dmsherazi/Battery-Management-System/gEDA-circuit-breaker/circuit-breaker-1.png

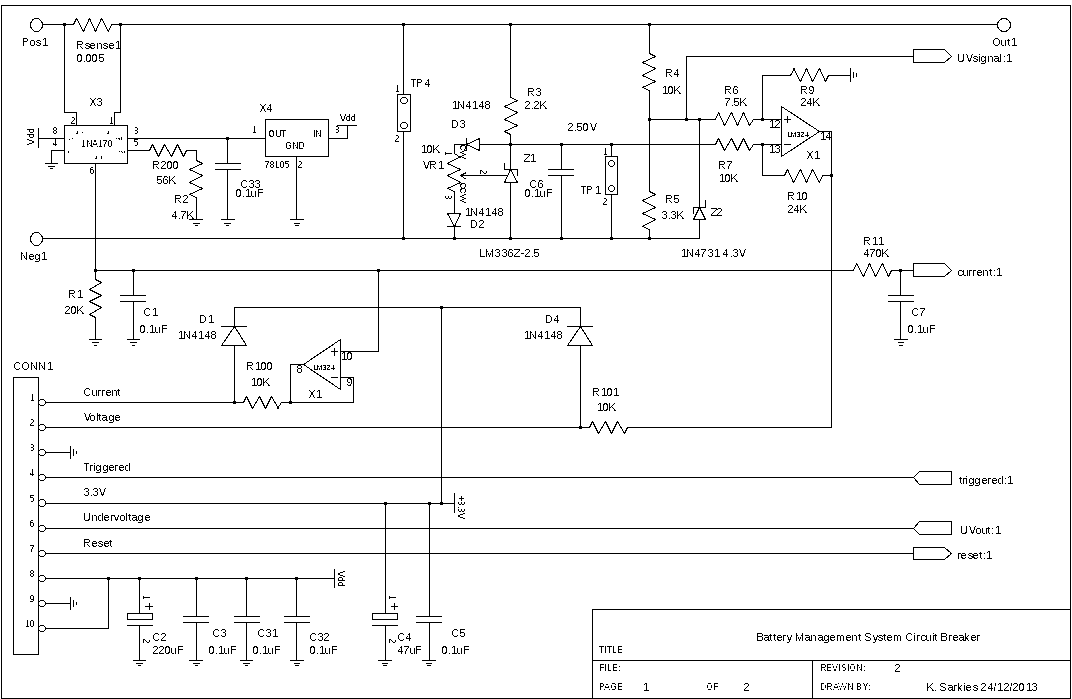
gEDA-circuit-breaker/circuit-breaker-1.png
