dmsherazi/Battery-Management-System/gEDA-circuit-breaker/circuit-breaker-2.png

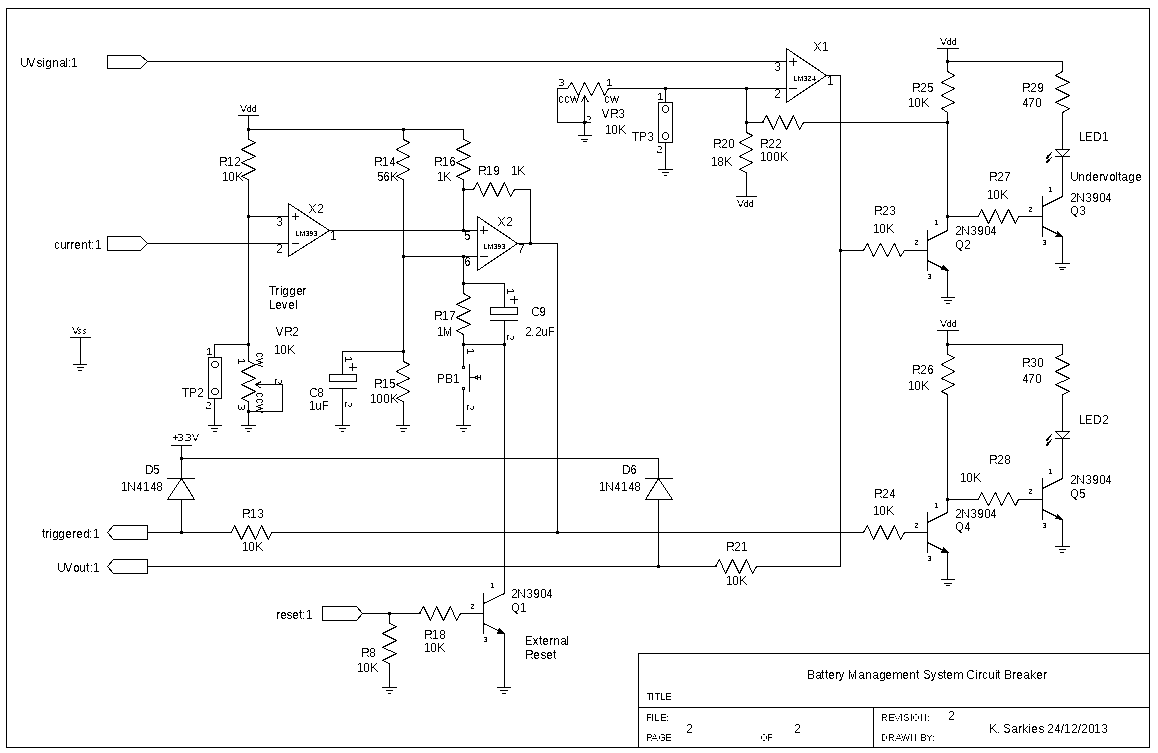
gEDA-circuit-breaker/circuit-breaker-2.png
