dmsherazi/Battery-Management-System/gEDA-circuit-breaker/circuit-breaker-pcb.png

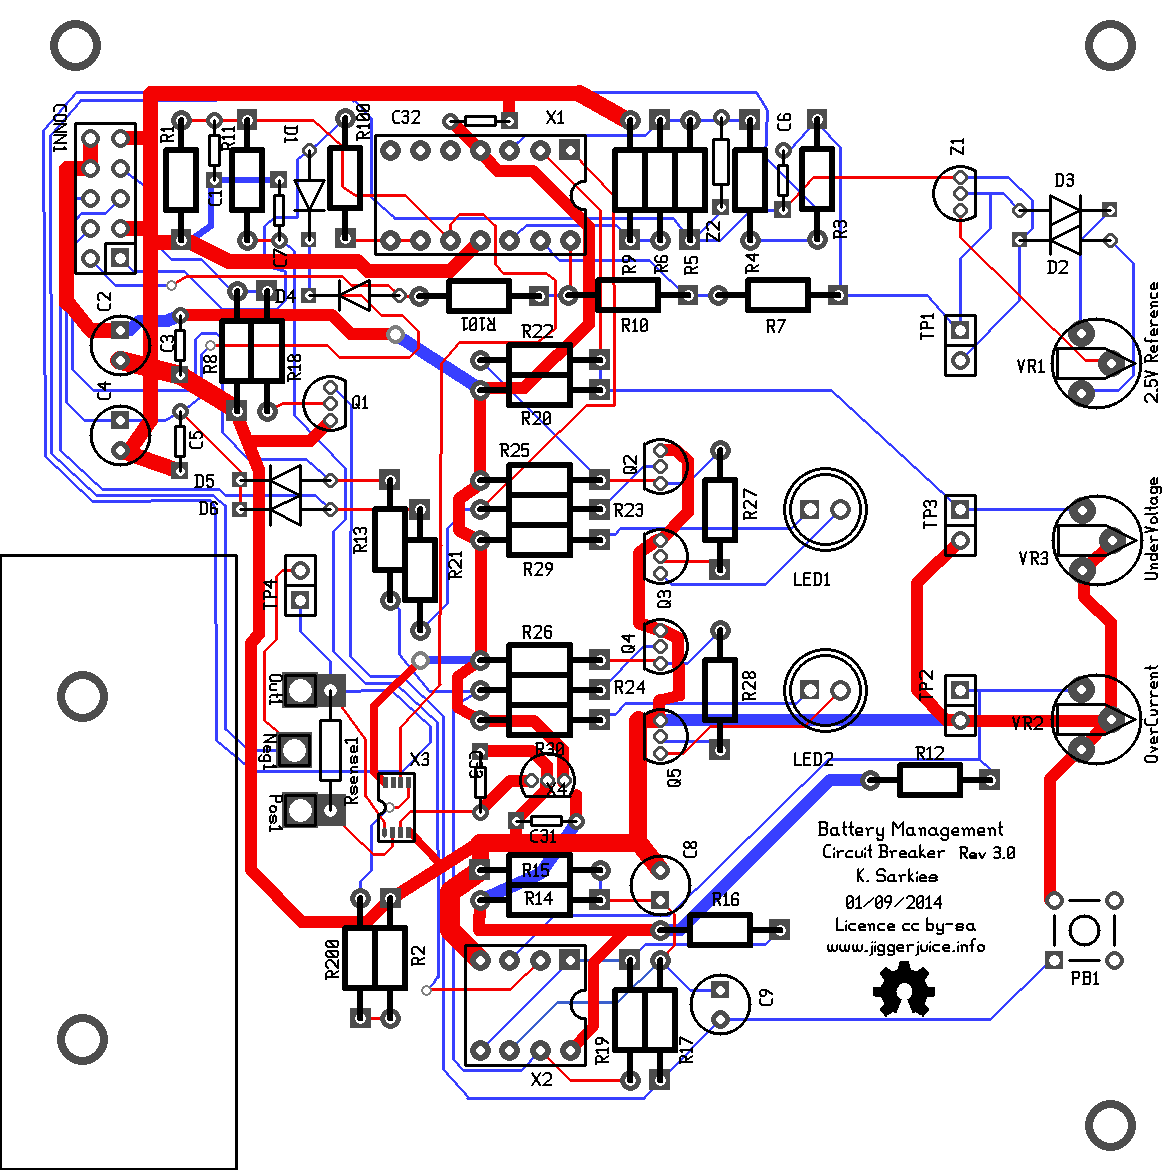
gEDA-circuit-breaker/circuit-breaker-pcb.png
