dmsherazi/Battery-Management-System/gEDA-interconnect/interconnect-connectors.png

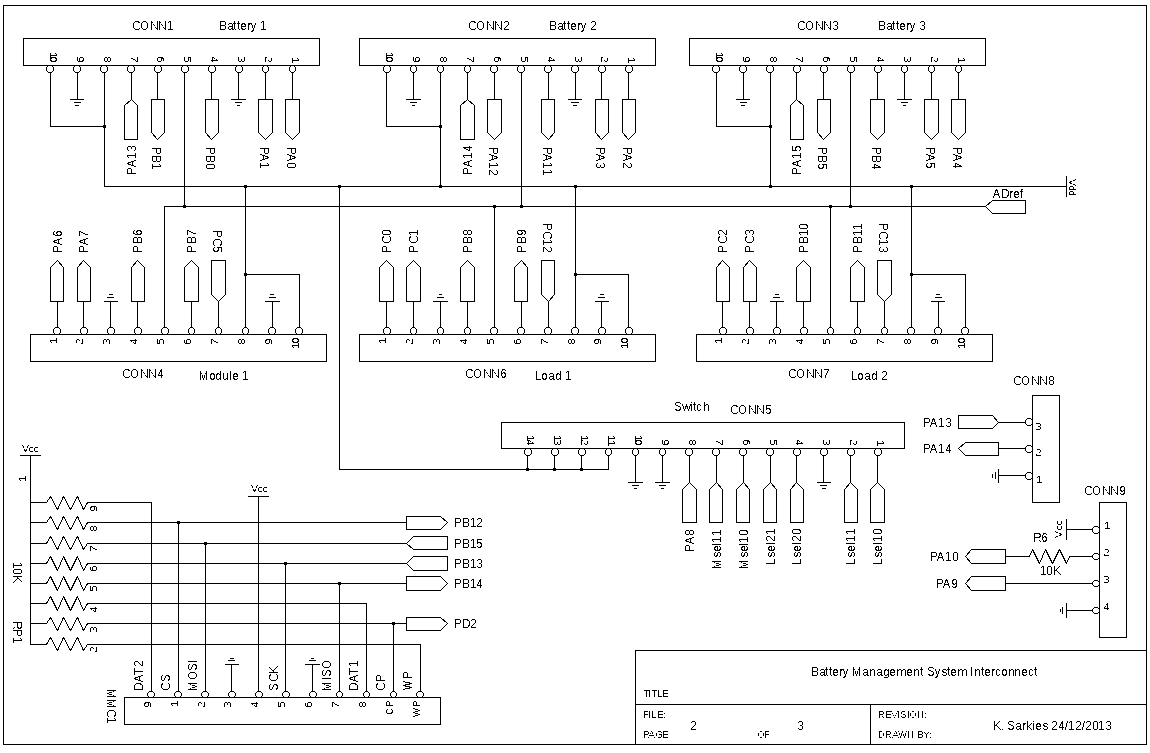
gEDA-interconnect/interconnect-connectors.png
