dmsherazi/Battery-Management-System/gEDA-switch/switch-mosfet.png

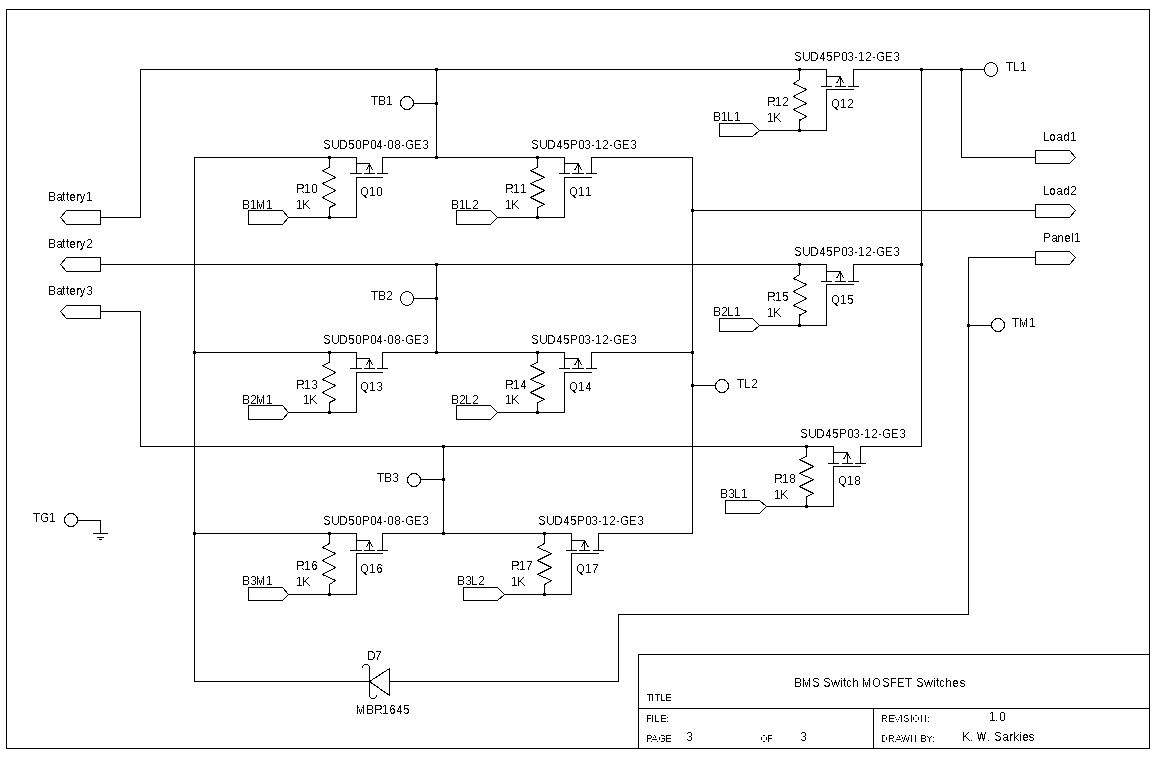
gEDA-switch/switch-mosfet.png
