dmsherazi/Battery-Management-System/gEDA-switch/switch-photo.jpg

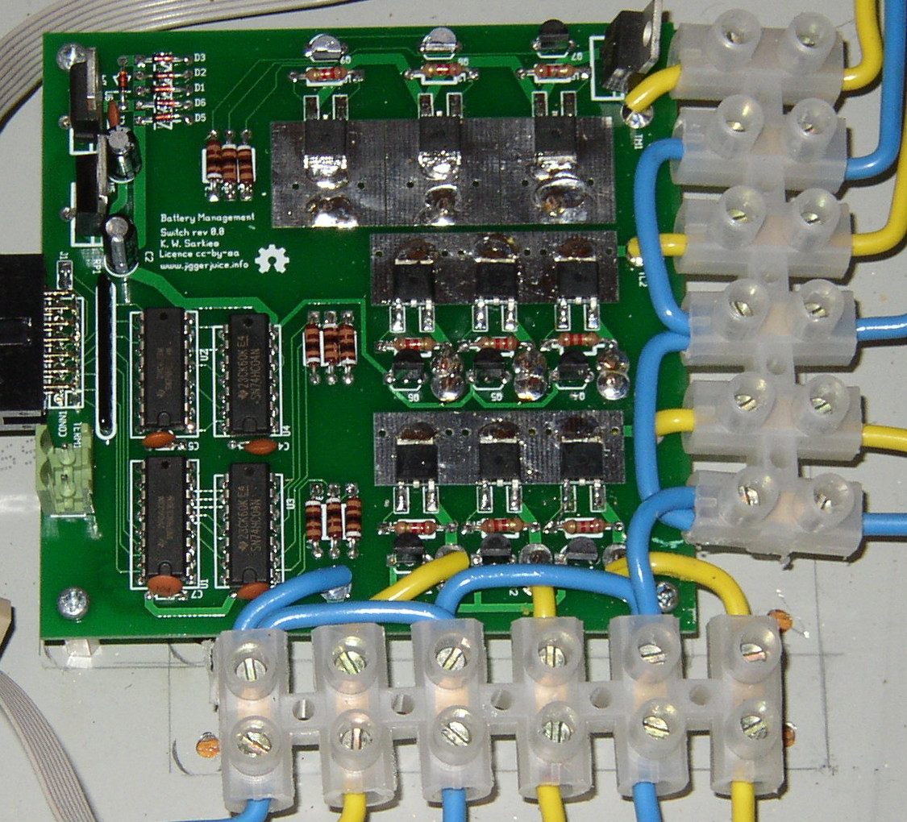
gEDA-switch/switch-photo.jpg
