dmsherazi/Battery-Management-System/gEDA-switch/switch-power.png

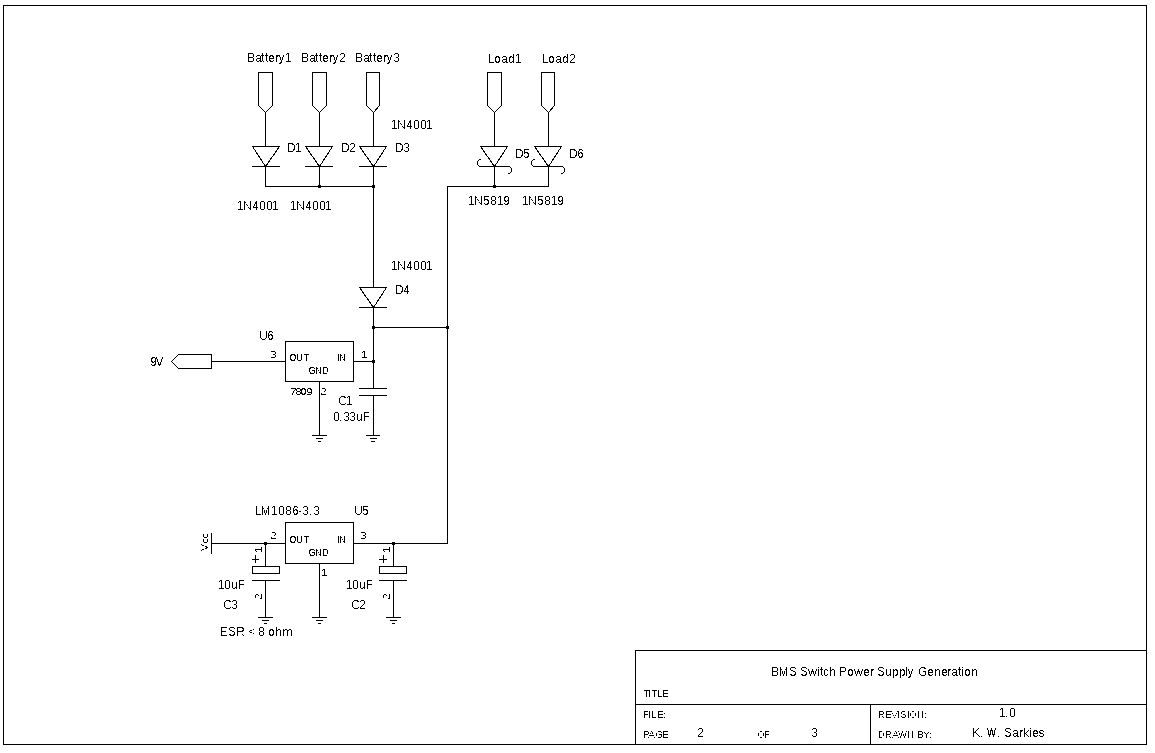
gEDA-switch/switch-power.png
