dmsherazi/Battery-Management-System/firmware-prot/power-management-objdic.c

/* STM32F1 Power Management for Solar Power

This file defines the CANopen object dictionary variables made available to an
external PC and to other processing modules which may be CANopen devices or
tasks running on the same microcontroller.

Note these definitions cannot be placed in the header file.
*/

/*
 * This file is part of the battery-management-system project.
 *
 * Copyright 2013 K. Sarkies <ksarkies@internode.on.net>
 *
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
 * You should have received a copy of the GNU Lesser General Public License
 * along with this program.  If not, see <http://www.gnu.org/licenses/>.
 */

#include <stdint.h>
#include <stdbool.h>

#include "FreeRTOS.h"
#include "power-management-objdic.h"
#include "power-management-hardware.h"

/* Byte pattern that indicates if a valid NVM config data block is present */
#define VALID_BLOCK                 0xD5

/* The rate at which the watchdog check is updated (1ms ticks) */
#define WATCHDOG_DELAY               ((portTickType)512/portTICK_RATE_MS)

/* The rate at which the charger algorithm is updated (1ms ticks) */
#define CHARGER_DELAY               ((portTickType)512/portTICK_RATE_MS)

/* The rate at which the monitoring is updated (1ms ticks) */
#define MONITOR_DELAY               ((portTickType)1024/portTICK_RATE_MS)

/* The default rate at which the samples are taken (1ms ticks) */
#define MEASUREMENT_DELAY           ((portTickType)512/portTICK_RATE_MS)

/* Delay to allow measurements to settle during the calibration sequence (1ms ticks) */
#define CALIBRATION_DELAY           ((portTickType)4096/portTICK_RATE_MS)

/* Preset the config data block in FLASH to a given pattern to indicate unused. */
union ConfigGroup configDataBlock __attribute__ ((section (".configBlock"))) = {{0xA5}};
union ConfigGroup configData;

/*--------------------------------------------------------------------------*/
/** @brief Initialise Global Configuration Variables

This determines if configuration variables are present in NVM, and if so
reads them in. The first entry is checked against a preprogrammed value to
determine if the block is a valid configuration block. This allows the program
to determine whether to use the block stored in FLASH or to use defaults.
*/

void setGlobalDefaults(void)
{
    flashReadData((uint32_t*)configDataBlock.data,
                   configData.data,sizeof(configData.config));
    if (configData.config.validBlock == VALID_BLOCK) return;
    configData.config.watchdogDelay = WATCHDOG_DELAY;
    configData.config.chargerDelay = CHARGER_DELAY;
    configData.config.measurementDelay = MEASUREMENT_DELAY;
    configData.config.monitorDelay = MONITOR_DELAY;
    configData.config.calibrationDelay = CALIBRATION_DELAY;
    configData.config.alphaR = 100;           /* about 0.4 */
    configData.config.alphaV = 256;           /* No Filter */
    configData.config.alphaC = 180;           /* about 0.7, only for detecting float state. */
/* Set default battery parameters */
    configData.config.batteryCapacity[0] = 54;
    configData.config.batteryCapacity[1] = 80;
    configData.config.batteryCapacity[2] = 54;
    configData.config.batteryType[0] = wetT;
    configData.config.batteryType[1] = gelT;
    configData.config.batteryType[2] = wetT;
    configData.config.monitorStrategy = 0xFF;
    uint8_t i=0;
    for (i=0; i<NUM_BATS; i++) setBatteryChargeParameters(i);
/* Zero the offsets. */
    for (i=0; i<NUM_IFS; i++) configData.config.currentOffsets.data[i] = 0;
/* Don't track unless instructed externally */
    configData.config.autoTrack = false;
    configData.config.debugMessageSend = false;
    configData.config.switchAvoidance = false;
}

/*--------------------------------------------------------------------------*/
/** @brief Write Configuration Data Block to Flash

Refer to the linker script for allocation of the config data block on a
page boundary. If this is not done, a page erase may destroy valid data or code.

The current datablock is written to flash with the first entry set to a value
that indicates whether the block is a valid programmed configuration block.

@returns result code. 0 success, 1 fail.
*/

uint32_t writeConfigBlock(void)
{
    configData.config.validBlock = VALID_BLOCK;
    return flashWriteData((uint32_t*)configDataBlock.data,
                          configData.data, sizeof(configData.config));
}

/*--------------------------------------------------------------------------*/
/** @brief Set the Battery Charge Parameters given the Type

@param[in] battery: 0..NUM_BATS-1
*/

void setBatteryChargeParameters(int battery)
{
    if (configData.config.batteryType[battery] == wetT)
    {
        configData.config.absorptionVoltage[battery] = 3712;        /* 14.5V */
        configData.config.floatVoltage[battery] = 3379;             /* 13.2V */
    }
    else if (configData.config.batteryType[battery] == agmT)
    {
        configData.config.absorptionVoltage[battery] = 3738;        /* 14.6V */
        configData.config.floatVoltage[battery] = 3482;             /* 13.6V */
    }
    else if (configData.config.batteryType[battery] == gelT)
    {
        configData.config.absorptionVoltage[battery] = 3610;        /* 14.1V */
        configData.config.floatVoltage[battery] = 3532;             /* 13.8V */
    }
    configData.config.floatStageCurrentScale[battery] = 50;
    configData.config.bulkCurrentLimitScale[battery] = 5;
}

/*--------------------------------------------------------------------------*/
/** @brief Provide the Battery Type

@param[in] battery: 0..NUM_BATS-1
*/

battery_Type getBatteryType(int battery)
{
    return configData.config.batteryType[battery];
}

/*--------------------------------------------------------------------------*/
/** @brief Provide the Battery Capacity

@param[in] battery: 0..NUM_BATS-1
*/

int16_t getBatteryCapacity(int battery)
{
    return configData.config.batteryCapacity[battery];
}

/*--------------------------------------------------------------------------*/
/** @brief Provide the Battery Bulk Current Limit

@param[in] battery: 0..NUM_BATS-1
*/

int16_t getBulkCurrentLimit(int battery)
{
    return configData.config.batteryCapacity[battery]*256/
            configData.config.bulkCurrentLimitScale[battery];
}

/*--------------------------------------------------------------------------*/
/** @brief Provide the Battery Float Current Cutoff

@param[in] battery: 0..NUM_BATS-1
*/

int16_t getFloatStageCurrent(int battery)
{
    return configData.config.batteryCapacity[battery]*256/
            configData.config.floatStageCurrentScale[battery];
}

/*--------------------------------------------------------------------------*/
/** @brief Provide the Absorption Phase Voltage Limit

@param[in] battery: 0..NUM_BATS-1
*/

int16_t getAbsorptionVoltage(int battery)
{
    return configData.config.absorptionVoltage[battery];
}
/*--------------------------------------------------------------------------*/
/** @brief Provide the Float Phase Voltage Limit

@param[in] battery: 0..NUM_BATS-1
*/

int16_t getFloatVoltage(int battery)
{
    return configData.config.floatVoltage[battery];
}

/*--------------------------------------------------------------------------*/
/** @brief Provide the Forgetting factor for Charger Voltage Smoothing

*/

int16_t getAlphaV(void)
{
    return configData.config.alphaV;
}

/*--------------------------------------------------------------------------*/
/** @brief Provide the Forgetting factor for Charger Current Smoothing

*/

int16_t getAlphaC(void)
{
    return configData.config.alphaC;
}

/*--------------------------------------------------------------------------*/
/** @brief Provide the Forgetting factor for Resistance Estimator Smoothing

*/

int16_t getAlphaR(void)
{
    return configData.config.alphaR;
}

/*--------------------------------------------------------------------------*/
/** @brief Provide the Current Offset

@parameter uint8_t interface: the interface 0...NUM_IFS.
*/

int16_t getCurrentOffset(uint8_t interface)
{
    return configData.config.currentOffsets.data[interface];
}

/*--------------------------------------------------------------------------*/
/** @brief Set the Current Offset

@parameter uint8_t interface: the interface 0...NUM_IFS.
@parameter uint16_t current offset value
*/

void setCurrentOffset(uint8_t interface, int16_t offset)
{
    configData.config.currentOffsets.data[interface] = offset;
}

/*--------------------------------------------------------------------------*/
/** @brief Provide the Watchdog Task Time Interval

This is the time between decision updates.
*/

portTickType getWatchdogDelay(void)
{
    return configData.config.watchdogDelay;
}

/*--------------------------------------------------------------------------*/
/** @brief Provide the Charging Task Time Interval

This is the time between decision updates.
*/

portTickType getChargerDelay(void)
{
    return configData.config.chargerDelay;
}

/*--------------------------------------------------------------------------*/
/** @brief Provide the Measurement Task Time Interval

This is the time between measurement updates.
*/

portTickType getMeasurementDelay(void)
{
    return configData.config.measurementDelay;
}

/*--------------------------------------------------------------------------*/
/** @brief Provide the Monitor Task Time Interval

This is the time between decision updates.
*/

portTickType getMonitorDelay(void)
{
    return configData.config.monitorDelay;
}

/*--------------------------------------------------------------------------*/
/** @brief Provide the Calibration Time Interval

This is the time between measurement updates.
*/

portTickType getCalibrationDelay(void)
{
    return configData.config.calibrationDelay;
}

/*--------------------------------------------------------------------------*/
/** @brief Recording switch

True if recording has been requested, false otherwise.
*/

bool isRecording(void)
{
    return configData.config.recording;
}

/*--------------------------------------------------------------------------*/
/** @brief Automatic Tracking switch

True if automatic tracking has been requested, false otherwise.
*/

bool isAutoTrack(void)
{
    return configData.config.autoTrack;
}

/*--------------------------------------------------------------------------*/
/** @brief Switch Avoidance

True if the switching avoidance strategy is requested.
*/

bool isSwitchAvoidance(void)
{
    return configData.config.switchAvoidance;
}

/*--------------------------------------------------------------------------*/
/** @brief Automatic Tracking switch

True if automatic tracking has been requested, false otherwise.
*/

uint8_t getMonitorStrategy(void)
{
    return configData.config.monitorStrategy;
}

/*--------------------------------------------------------------------------*/
/** @brief Return a status word showing software controls.

bit 0 if autoTrack,
bit 1 if recording,
bit 2 if switch avoidance
bit 3 if measurements are being sent
bit 4 if debug messages are being sent

@returns uint16_t status of controls
*/
uint16_t getControls(void)
{
    uint8_t controls = 0;
    if (configData.config.autoTrack) controls |= 1<<0;
    if (configData.config.recording) controls |= 1<<1;
    if (configData.config.switchAvoidance) controls |= 1<<2;
    if (configData.config.measurementSend) controls |= 1<<3;
    if (configData.config.debugMessageSend) controls |= 1<<4;
    return controls;
}
