dmsherazi/Battery-Management-System/firmware/power-management-comms.c

/* STM32F1 Power Management for Solar Power

Defines the Communications Task and library

This task receives incoming characters and assembles them into a command line.
The command is then interpreted and executed.
Commands include file operations, switch settings, all parameter settings.
The library consists of all routines needed by other tasks to communicate.

The communication medium is non-specific, referring on to the hardware module.

This task is the only one having write access to the object dictionary items.

Initial 29 September 2013
*/

/*
 * This file is part of the battery-management-system project.
 *
 * Copyright 2013 K. Sarkies <ksarkies@internode.on.net>
 *
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
 * You should have received a copy of the GNU Lesser General Public License
 * along with this program.  If not, see <http://www.gnu.org/licenses/>.
 */

#include <stdint.h>
#include <stdbool.h>

/* Scheduler includes. */
#include "FreeRTOS.h"
#include "task.h"
#include "queue.h"
#include "semphr.h"
#include "timers.h"

#include "power-management-hardware.h"
#include "power-management-objdic.h"
#include "power-management-file.h"
#include "power-management-measurement.h"
#include "power-management-monitor.h"
#include "power-management-charger.h"
#include "power-management-time.h"
#include "power-management-lib.h"
#include "power-management-comms.h"
#include "ff.h"

/*--------------------------------------------------------------------------*/
/* Local Prototypes */
static void initGlobals(void);
static void parseCommand(uint8_t* line);
static void resetCallback(xTimerHandle resethandle);
static void lapseCommsCallback(xTimerHandle lapseCommsTimer);
void commsPrintInt(int32_t value);
void commsPrintHex(uint32_t value);
void commsPrintString(char *ch);
void commsPrintChar(char *ch);

/*--------------------------------------------------------------------------*/
/* Global Variables */
/* These configuration variables are part of the Object Dictionary. */
/* This is defined in power-management-objdic and is updated in response to
received messages. */
extern union ConfigGroup configData;

/* FreeRTOS queues and intercommunication variables */
/* Serial Comms defined here */
/* The semaphore must be used to protect messages until they have been queued
in their entirety. This is done in convenience functions defined below */
xQueueHandle commsSendQueue, commsReceiveQueue;
xSemaphoreHandle commsSendSemaphore, commsEmptySemaphore;
/* FreeRTOS queue to receive command responses, defined in File */
extern xQueueHandle fileReceiveQueue;
extern xSemaphoreHandle fileSendSemaphore;

/*--------------------------------------------------------------------------*/
/* Local Variables */
static uint8_t intf;
static char writeFileName[12];
static char readFileName[12];
static uint8_t writeFileHandle;
static uint8_t readFileHandle;
static int lapseCommsID;
static xTimerHandle lapseCommsTimer;

/*--------------------------------------------------------------------------*/
/* @brief Communications Receive Task

This collects characters received over the communications interface and packages
them into a line for action as a command.
*/

void prvCommsTask( void *pvParameters )
{
    static uint8_t line[80];
    static uint8_t characterPosition = 0;

    initGlobals();

/* Timer to cause communications to cease if nothing received for 10 seconds */
    lapseCommsTimer = xTimerCreate("Lapse Comms",10000,pdFALSE,0,lapseCommsCallback);

    while(1)
    {
/* Build a command line string before actioning. The task will block
indefinitely waiting for input. */
        char character;
        xQueueReceive(commsReceiveQueue,&character,portMAX_DELAY);
        if ((character == 0x0D) || (character == 0x0A) || (characterPosition > 78))
        {
            if (lapseCommsTimer != NULL) xTimerReset(lapseCommsTimer,0);
            line[characterPosition] = 0;
            characterPosition = 0;
            parseCommand(line);
        }
        else line[characterPosition++] = character;
    }
}

/*--------------------------------------------------------------------------*/
/* @brief Initialize

This initializes the queues and semaphores used by the task.
*/

void initComms(void)
{
/* Setup the queues to use */
    commsSendQueue = xQueueCreate(COMMS_QUEUE_SIZE,1);
    commsReceiveQueue = xQueueCreate(COMMS_QUEUE_SIZE,1);
    commsSendSemaphore = xSemaphoreCreateBinary();
    xSemaphoreGive(commsSendSemaphore);
    commsEmptySemaphore = xSemaphoreCreateBinary();
    xSemaphoreGive(commsEmptySemaphore);
}

/*--------------------------------------------------------------------------*/
/** @brief Initialise Global Variables

*/

static void initGlobals(void)
{
/* File name and handle variables are carried globally from the time of creation */
    writeFileName[0] = 0;
    readFileName[0] = 0;
    writeFileHandle = 0xFF;
    readFileHandle = 0xFF;
}

/*--------------------------------------------------------------------------*/
/** @brief Parse a command line and act on it.

Commands begin with a lower case letter a, d, p or f followed by an upper case
command letter.

Unrecognizable messages should just be discarded.

@param[in] char *line: the command line in ASCII
*/

static void parseCommand(uint8_t* line)
{
/* ======================== Action commands ========================  */
    if (line[0] == 'a')
    {
/* Snm Manually set Switch.
S followed by battery (1-3, 0 = none) and load (0-1)/panel (2).
Each two-bit field represents a load or panel, and the setting is the
battery to be connected (no two batteries can be connected to a load/panel).
The final bit pattern of settings go into PB8-13.
Preserve the lower 8 bits. */
        switch (line[1])
        {
        case 'S':
            {
                uint8_t battery = line[2]-'0';
                uint8_t setting = line[3]-'0'-1;
                if ((battery < 4) && (setting < 4)) setSwitch(battery, setting);
                if (setting == 2) setPanelSwitchSetting(battery);
                break;
            }
/* R Reset a tripped overcurrent circuit breaker.
Set a FreeRTOS timer to expire after 500ms at which time the reset line is
released. The command is followed by an interface number 0-5 being batteries
1-3, loads 1-2 and module. */
        case 'R':
            {
                portTickType resetTime = 500;
                intf = line[2]-'0';
                if (intf > NUM_IFS-1) break;
                xTimerHandle resetHandle
                    = xTimerCreate("Reset",resetTime,pdFALSE,(void *)intf,resetCallback);
                if(resetHandle == NULL) break;
                if (xTimerStart(resetHandle,0) != pdPASS) break;
                overCurrentReset(intf);
                break;
            }
/* Write the current configuration block to FLASH */
        case 'W':
            {
                writeConfigBlock();
                break;
            }
/* Send an ident response */
        case 'E':
            {
                char ident[35] = "Battery Management System,";
                stringAppend(ident,FIRMWARE_VERSION);
                stringAppend(ident,",");
                char version[3];
                intToAscii(VERSION,version);
                stringAppend(ident,version);
                sendStringLowPriority("dE",ident);
                break;
            }
/* Set the battery SoC from the OCV */
        case 'B':
            {
                uint8_t battery = line[2]-'1';
                setBatterySoC(battery,computeSoC(getBatteryVoltage(battery),
                           getTemperature(),getBatteryType(battery)));
                break;
            }
        }
    }
/* ======================== Data request commands ================  */
    else if (line[0] == 'd')
    {
        switch (line[1])
        {
/* S Ask for all switch settings to be sent as well as control settings. */
        case 'S':
            {
                sendResponse("dS",(int)getSwitchControlBits());
                uint8_t controlByte = getControls();
                sendResponse("dD",controlByte);
                break;
            }
/* Bn Ask for battery parameters to be sent */
        case 'B':
            {
                char id[] = "pR0";
                id[2] = line[2];
                uint8_t battery = line[2] - '1';
                dataMessageSend(id,getBatteryResistanceAv(battery),0);
                id[1] = 'T';
                dataMessageSend(id,(int32_t)configData.config.batteryType[battery],
                                   (int32_t)configData.config.batteryCapacity[battery]);
                id[1] = 'F';
                dataMessageSend(id,(int32_t)configData.config.
                                            floatStageCurrentScale[battery],
                                   (int32_t)configData.config.floatVoltage[battery]);
                id[1] = 'A';
                dataMessageSend(id,(int32_t)configData.config.
                                            bulkCurrentLimitScale[battery],
                                   (int32_t)configData.config.absorptionVoltage[battery]);
                break;
            }
/* T Ask for monitor strategy parameters to be sent. */
        case 'T':
            {
                char id[] = "pts";
                dataMessageSend(id,(int32_t)configData.config.monitorStrategy,0);
                id[2] = 'V';
                dataMessageSend(id,(int32_t)configData.config.lowVoltage,
                                   (int32_t)configData.config.criticalVoltage);
                id[2] = 'S';
                dataMessageSend(id,(int32_t)configData.config.lowSoC,
                                   (int32_t)configData.config.criticalSoC);
                id[2] = 'F';
                dataMessageSend(id,(int32_t)configData.config.floatBulkSoC,0);
                break;
            }
/* C Ask for charger strategy parameters to be sent. */
        case 'C':
            {
                char id[] = "pcs";
                dataMessageSend(id,(int32_t)configData.config.chargerStrategy,0);
                id[2] = 'R';
                dataMessageSend(id,(int32_t)configData.config.restTime,
                                   (int32_t)configData.config.absorptionTime);
                id[2] = 'D';
                dataMessageSend(id,(int32_t)configData.config.minDutyCycle,0);
                id[2] = 'F';
                dataMessageSend(id,(int32_t)configData.config.floatTime,
                                   (int32_t)configData.config.floatBulkSoC);
                break;
            }
        }
    }
/* ================ Parameter setting commands ================  */
    else if (line[0] == 'p')
    {
        uint8_t battery = line[2]-'1';
        switch (line[1])
        {
/* a-, a+ Turn autoTracking on or off */
        case 'a':
            {
                if (line[2] == '-') configData.config.autoTrack = false;
                else if (line[2] == '+') configData.config.autoTrack = true;
                break;
            }
/* c-, c+ Turn communications sending on or off */
        case 'c':
            {
                if (line[2] == '-') configData.config.enableSend = false;
                else if (line[2] == '+') configData.config.enableSend = true;
                break;
            }
/* C Start a calibration sequence */
        case 'C':
            {
                startCalibration();
                break;
            }
/* d Turn on debug messages */
        case 'd':
            {
                if (line[2] == '+') configData.config.debugMessageSend = true;
                if (line[2] == '-') configData.config.debugMessageSend = false;
                break;
            }
/* Hxx Set time from an ISO 8601 formatted string. */
        case 'H':
            {
                setTimeFromString((char*)line+2);
                break;
            }
/* M-, M+ Turn on/off data messaging (mainly for debug) */
        case 'M':
            {
                if (line[2] == '-') configData.config.measurementSend = false;
                else if (line[2] == '+') configData.config.measurementSend = true;
                break;
            }
/* r-, r+ Turn recording on or off */
        case 'r':
            {
                if (line[2] == '-') configData.config.recording = false;
                else if ((line[2] == '+') && (writeFileHandle < 0x0FF))
                    configData.config.recording = true;
                break;
            }
/*--------------------*/
/* BATTERY parameters */
/* Tntxx Set battery type and capacity, n is battery, t is type, xx is capacity */
        case 'T':
            {
                if (battery < 3)
                {
                    uint8_t type = line[3]-'0';
                    if (type < 3)
                    {
                        configData.config.batteryType[battery] =
                            (battery_Type)type;
                        configData.config.batteryCapacity[battery] =
                            asciiToInt((char*)line+4);
                        setBatteryChargeParameters(battery);
                    }
                }
                break;
            }
/* m-, m+ Turn on/off battery missing */
        case 'm':
            {
                if (line[3] == '-') setBatteryMissing(battery,false);
                else if (line[3] == '+') setBatteryMissing(battery,true);
                break;
            }
/* Inxx Set bulk current limit, n is battery, xx is limit */
        case 'I':
            {
                if (battery < 3)
                    configData.config.bulkCurrentLimitScale[battery] =
                        asciiToInt((char*)line+3);
                break;
            }
/* Anxx Set battery gassing voltage limit, n is battery, xx is limit */
        case 'A':
            {
                if (battery < 3)
                    configData.config.absorptionVoltage[battery] =
                        asciiToInt((char*)line+3);
                break;
            }
/* fnxx Set battery float current trigger, n is battery, xx is trigger */
        case 'f':
            {
                if (battery < 3)
                    configData.config.floatStageCurrentScale[battery] =
                        asciiToInt((char*)line+3);
                break;
            }
/* Fnxx Set battery float voltage limit, n is battery, xx is limit */
        case 'F':
            {
                if (battery < 3)
                    configData.config.floatVoltage[battery] =
                        asciiToInt((char*)line+3);
                break;
            }
/* z zero current calibration by forcing current offset. */
        case 'z':
            {
                if (battery < 3)
                    setCurrentOffset(battery,getCurrent(battery));
                break;
            }
/*--------------------*/
/* MONITOR parameters */
/* sn Set monitor strategy byte n for keeping isolation or avoiding loading
the battery under charge. */
        case 's':
            {
                uint8_t monitorStrategy = line[2]-'0';
                if (monitorStrategy <= 3)
                    configData.config.monitorStrategy = monitorStrategy;
                break;
            }
/* vx set low voltage threshold, x is voltage times 256. */
        case 'v':
            {
                configData.config.lowVoltage = asciiToInt((char*)line+2);
                break;
            }
/* Vx set critical voltage threshold, x is voltage times 256. */
        case 'V':
            {
                configData.config.criticalVoltage = asciiToInt((char*)line+2);
                break;
            }
/* xx set low SoC threshold, x is voltage times 256. */
        case 'x':
            {
                configData.config.lowSoC = asciiToInt((char*)line+2);
                break;
            }
/* Xx set critical SoC threshold, x is voltage times 256. */
        case 'X':
            {
                configData.config.criticalSoC = asciiToInt((char*)line+2);
                break;
            }
/*--------------------*/
/* CHARGER parameters */
/* Sx set charger strategy. */
        case 'S':
            {
                uint8_t chargerStrategy = line[2]-'0';
                if (chargerStrategy < 2)
                    configData.config.chargerStrategy = chargerStrategy;
                break;
            }
/* Rx set charger algorithm minimum rest time in seconds. */
        case 'R':
            {
                configData.config.restTime = asciiToInt((char*)line+2);
                break;
            }
/* Ax set charger algorithm minimum gassing phase time in seconds.. */
        case 'G':
            {
                configData.config.absorptionTime = asciiToInt((char*)line+2);
                break;
            }
/* Dx set charger minimum duty cycle. */
        case 'D':
            {
                configData.config.minDutyCycle = asciiToInt((char*)line+2);
                break;
            }
/* Fx set charger time to float in seconds. */
        case 'e':
            {
                configData.config.floatTime = asciiToInt((char*)line+2);
                break;
            }
/* Bx set charger SoC to change float to bulk. */
        case 'B':
            {
                configData.config.floatBulkSoC = asciiToInt((char*)line+2);
                break;
            }
        }
    }
/* ======================== File commands ================ */
/*
F           - get free clusters
Wfilename   - Open file for read/write. Filename is 8.3 string style. Returns handle.
Rfilename   - Open file read only. Filename is 8.3 string style. Returns handle.
Xfilename   - Delete the file. Filename is 8.3 string style.
Cxx         - Close file. x is the file handle.
Gxx         - Read a record from read or write file.
Ddirname    - Get a directory listing. Directory name is 8.3 string style.
d[dirname]  - Get the first (if dirname present) or next entry in directory.
s           - Get status of open files and configData.config.recording flag
M           - Mount the SD card.
All commands return an error status byte at the end.
Only one file for writing and a second for reading is possible.
Data is not written to the file externally. */
    else if (line[0] == 'f')
    {
        switch (line[1])
        {
/* Return number of free clusters followed by the cluster size in bytes. */
            case 'F':
            {
                uint8_t wordBuf;
                uint32_t freeClusters = 0;
                uint32_t sectorCluster = 0;
                uint8_t fileStatus = FR_INT_ERR;
                if (xSemaphoreTake(fileSendSemaphore,COMMS_FILE_TIMEOUT))
                {
                    sendFileCommand('F',0,line+2);
                    uint8_t i;
                    for (i=0; i<4; i++)
                    {
                        wordBuf = 0;
                        xQueueReceive(fileReceiveQueue,&wordBuf,portMAX_DELAY);
                        freeClusters |= (wordBuf << 8*i);
                    }
                    for (i=0; i<4; i++)
                    {
                        wordBuf = 0;
                        xQueueReceive(fileReceiveQueue,&wordBuf,portMAX_DELAY);
                        sectorCluster |= (wordBuf << 8*i);
                    }
                    dataMessageSend("fF",freeClusters,sectorCluster);
                    xQueueReceive(fileReceiveQueue,&fileStatus,portMAX_DELAY);
                    xSemaphoreGive(fileSendSemaphore);
                }
                sendResponse("fE",(uint8_t)fileStatus);
                break;
            }
/* Open a file for writing */
            case 'W':
            {
                if (stringLength((char*)line+2) < 12)
                {
                    uint8_t fileStatus = FR_INT_ERR;
                    if (xSemaphoreTake(fileSendSemaphore,COMMS_FILE_TIMEOUT))
                    {
                        stringCopy(writeFileName,(char*)line+2);
                        sendFileCommand('W',13,line+2);
                        xQueueReceive(fileReceiveQueue,&writeFileHandle,portMAX_DELAY);
                        sendResponse("fW",writeFileHandle);
                        xQueueReceive(fileReceiveQueue,&fileStatus,portMAX_DELAY);
                        xSemaphoreGive(fileSendSemaphore);
                    }
                    sendResponse("fE",(uint8_t)fileStatus);
                }
                break;
            }
/* Open a file for Reading */
            case 'R':
            {
                if (stringLength((char*)line+2) < 12)
                {
                    uint8_t fileStatus = FR_INT_ERR;
                    if (xSemaphoreTake(fileSendSemaphore,COMMS_FILE_TIMEOUT))
                    {
                        stringCopy(readFileName,(char*)line+2);
                        sendFileCommand('R',13,line+2);
                        xQueueReceive(fileReceiveQueue,&readFileHandle,portMAX_DELAY);
                        sendResponse("fR",readFileHandle);
                        xQueueReceive(fileReceiveQueue,&fileStatus,portMAX_DELAY);
                        xSemaphoreGive(fileSendSemaphore);
                    }
                    sendResponse("fE",(uint8_t)fileStatus);
                }
                break;
            }
/* Close file for write or read file. The file handle is a two character integer. */
            case 'C':
            {
                uint8_t fileStatus = FR_INT_ERR;
                if (xSemaphoreTake(fileSendSemaphore,COMMS_FILE_TIMEOUT))
                {
                    uint8_t fileHandle = asciiToInt((char*)line+2);
                    sendFileCommand('C',1,&fileHandle);
                    xQueueReceive(fileReceiveQueue,&fileStatus,portMAX_DELAY);
                    if (fileStatus == FR_OK)
                    {
                        if (writeFileHandle == fileHandle) writeFileHandle = 0xFF;
                        else if (readFileHandle == fileHandle) readFileHandle = 0xFF;
                    }
                    xSemaphoreGive(fileSendSemaphore);
                }
                sendResponse("fE",(uint8_t)fileStatus);
                break;
            }
/* Read a record of data from the read or write file. The data starts from the
end of the previous block that was read (or the file start if just opened).
The file handle is a two character integer. A block of bytes is read from
the file and stored in a circular buffer. A record is taken from this block and
sent, the rest remains in the buffer until the next request. */
#define GET_RECORD_SIZE 80
            case 'G':
            {
                uint8_t fileStatus = FR_INT_ERR;
                if (xSemaphoreTake(fileSendSemaphore,COMMS_FILE_TIMEOUT))
                {
                    int numberRecords = asciiToInt((char*)line+2);
                    if (numberRecords < 1) numberRecords = 1;
                    static FRESULT fileStatus = FR_OK;
                    static uint8_t buffer[GET_RECORD_SIZE];
                    static uint8_t readPointer = 0;
                    static uint8_t writePointer = 0;
                    char sendData[GET_RECORD_SIZE];
                    uint8_t sendPointer = 0;
                    uint8_t fileHandle = asciiToInt((char*)line+2);
                    uint8_t blockLength = GET_RECORD_SIZE-1;
                    uint8_t numRead;
                    uint8_t parameters[2] = {fileHandle, blockLength};
                    while (numberRecords > 0)
                    {
/* The buffer is empty, so fill up. */
                        if (readPointer == writePointer)
                        {
                            sendFileCommand('G',2,parameters);
                            numRead = 0;
                            xQueueReceive(fileReceiveQueue,&numRead,portMAX_DELAY);
/* As records are written in entirety, premature EOF should not happen. */
                            if (numRead != blockLength)
                            {
                                fileStatus = FR_DENIED;
                                break;
                            }
                            uint8_t i;
/* Read the entire block to the local buffer. */
                            for (i=0; i<numRead; i++)
                            {
                                uint8_t nextWritePointer = (writePointer+1)
                                                % GET_RECORD_SIZE;
                                xQueueReceive(fileReceiveQueue,
                                    buffer+writePointer,portMAX_DELAY);
                                writePointer = nextWritePointer;
                            }
/* Get status byte. */
                            xQueueReceive(fileReceiveQueue,&fileStatus,portMAX_DELAY);
                        }
/* Assemble the data message until EOL encountered, or block exhausted. */
                        while (sendPointer < GET_RECORD_SIZE-1)
                        {
                            sendData[sendPointer] = buffer[readPointer];
                            readPointer = (readPointer+1) % GET_RECORD_SIZE;
                            if (sendData[sendPointer] == '\n')
                            {
                                sendData[sendPointer+1] = 0;
                                sendString("fG",sendData);
                                sendPointer = 0;
                                numberRecords--;
                                break;
                            }
/* If the current block is exhausted, go get some more. */
                            if (readPointer == writePointer) break;
                            sendPointer++;
                        }
                    }
                    xSemaphoreGive(fileSendSemaphore);
                }
/* Status sent is from the last time the file was read. */
                sendResponse("fE",(uint8_t)fileStatus);
                break;
            }
/* Get a directory listing. Gets all items in the directory and sends the
type,size and name, each group preceded by a comma. The file command requests
each entry in turn, terminated by a null filename when the directory listing
is exhausted. */
            case 'D':
            {
                if (! xSemaphoreTake(commsSendSemaphore,COMMS_SEND_TIMEOUT))
                    break;
                uint8_t fileStatus = FR_INT_ERR;
                if (xSemaphoreTake(fileSendSemaphore,COMMS_FILE_TIMEOUT))
                {
                    char firstCharacter;
                    sendFileCommand('D',13,line+2);
                    commsPrintString("fD");
                    do
                    {
                        char type = 0;
/* Single character entry type */
                        xQueueReceive(fileReceiveQueue,&type,portMAX_DELAY);
                        char character;
/* Four bytes of file size */
                        uint32_t fileSize = 0;
                        uint8_t i;
                        for (i=0; i<4; i++)
                        {
                            character = 0;
                            xQueueReceive(fileReceiveQueue,&character,portMAX_DELAY);
                            fileSize = (fileSize << 8) + character;
                        }
/* Filename. If the first character of name is zero then the listing is ended */
                        character = 0;
                        xQueueReceive(fileReceiveQueue,&character,portMAX_DELAY);
                        firstCharacter = character;
                        if (firstCharacter > 0)
                        {
                            commsPrintString(",");
                            commsPrintChar(&type);
                            commsPrintHex(fileSize >> 16);
                            commsPrintHex(fileSize & 0xFFFF);
                            while (character > 0)
                            {
                                commsPrintChar(&character);
                                character = 0;
                                xQueueReceive(fileReceiveQueue,&character,portMAX_DELAY);
                            }
/* End of directory entry. Discard the status byte */
                            xQueueReceive(fileReceiveQueue,&fileStatus,portMAX_DELAY);
                            uint8_t eol = 0;
/* Send a zero parameter to ask for the next entry */
                            sendFileCommand('D',1,&eol);
                        }
                    }
                    while (firstCharacter > 0);
                    commsPrintString("\r\n");
                    xQueueReceive(fileReceiveQueue,&fileStatus,portMAX_DELAY);
                    xSemaphoreGive(fileSendSemaphore);
                }
                xSemaphoreGive(commsSendSemaphore);
                sendResponse("fE",(uint8_t)fileStatus);
                break;
            }
/* Return the next entry in the directory listing. If a directory name is sent,
then return the first entry. If the name has a zero in the first position,
return the next entry in the directory listing.
Returns the type, size and name preceded by a comma for compatibility with
the full directory listing request. If there are no further entries found in the
directory, then an empty string is sent back. */
            case 'd':
            {
                if (! xSemaphoreTake(commsSendSemaphore,COMMS_SEND_TIMEOUT))
                    break;
                uint8_t fileStatus = FR_INT_ERR;
                if (xSemaphoreTake(fileSendSemaphore,COMMS_FILE_TIMEOUT))
                {
                    sendFileCommand('D',13,line+2);
                    commsPrintString("fd");
                    char type = 0;
/* Single character entry type */
                    xQueueReceive(fileReceiveQueue,&type,portMAX_DELAY);
                    char character;
/* Four bytes of file size */
                    uint32_t fileSize = 0;
                    uint8_t i;
                    for (i=0; i<4; i++)
                    {
                        character = 0;
                        xQueueReceive(fileReceiveQueue,&character,portMAX_DELAY);
                        fileSize = (fileSize << 8) + character;
                    }
/* Filename. If the first character of name is zero then the listing is ended */
                    character = 0;
                    xQueueReceive(fileReceiveQueue,&character,portMAX_DELAY);
                    if (character > 0)  /* Pull in remaining characters of name */
                    {
                        commsPrintString(",");
                        commsPrintChar(&type);
                        commsPrintHex(fileSize >> 16);
                        commsPrintHex(fileSize & 0xFFFF);
                        while (character > 0)
                        {
                            commsPrintChar(&character);
                            character = 0;
                            xQueueReceive(fileReceiveQueue,&character,portMAX_DELAY);
                        }
                    }
                    commsPrintString("\r\n");
                    xQueueReceive(fileReceiveQueue,&fileStatus,portMAX_DELAY);
                    xSemaphoreGive(fileSendSemaphore);
                }
                xSemaphoreGive(commsSendSemaphore);
                sendResponse("fE",(uint8_t)fileStatus);
                break;
            }
/* Register (mount) the SD card. */
            case 'M':
            {
                uint8_t fileStatus = FR_INT_ERR;
                if (xSemaphoreTake(fileSendSemaphore,COMMS_FILE_TIMEOUT))
                {
                    sendFileCommand('M',0,line+2);
                    xQueueReceive(fileReceiveQueue,&fileStatus,portMAX_DELAY);
                    xSemaphoreGive(fileSendSemaphore);
                }
                sendResponse("fE",(uint8_t)fileStatus);
                break;
            }
/* Send a status message containing: software switches
(configData.config.recording), names of open files. */
            case 's':
            {
                if (! xSemaphoreTake(commsSendSemaphore,COMMS_SEND_TIMEOUT))
                    break;;
                commsPrintString("fs,");
                commsPrintInt((int)getControls());
                commsPrintString(",");
                uint8_t writeStatus;
                commsPrintInt(writeFileHandle);
                commsPrintString(",");
                if (writeFileHandle < 0xFF)
                {
                    commsPrintString(writeFileName);
                    commsPrintString(",");
                }
                commsPrintInt(readFileHandle);
                if (readFileHandle < 0xFF)
                {
                    commsPrintString(",");
                    commsPrintString(readFileName);
                }
                commsPrintString("\r\n");
                xSemaphoreGive(commsSendSemaphore);
                break;
            }
/* Delete a designated file. The file must not be open at the time.
A status is returned to signal a directory refresh. */
            case 'X':
            {
                uint8_t fileStatus = FR_INT_ERR;
                if (xSemaphoreTake(fileSendSemaphore,COMMS_FILE_TIMEOUT))
                {
                    sendFileCommand('X',13,line+2);
                    xQueueReceive(fileReceiveQueue,&fileStatus,portMAX_DELAY);
                    xSemaphoreGive(fileSendSemaphore);
                }
                sendResponse("fE",(uint8_t)fileStatus);
                break;
            }
        }
    }
}

/*--------------------------------------------------------------------------*/
/** @brief Reset Timer Callback

This is called when the timer on the overcurrent reset line expires. It releases
all reset lines. The assumption is that a reset called externally will be released
before a new call to reset is issued.

@note: the timer handle passed through the FreeRTSO timer call did not work so a
global is used until this is fixed.
*/

void resetCallback(xTimerHandle resetHandle)
{
    overCurrentRelease(intf);
}

/*--------------------------------------------------------------------------*/
/** @brief Send a data message with two parameters

This is an asynchronous TxPDO in CANopen and therefore is nominally of fixed
length. The response parameters are converted to ASCII integer for debug.

This will abandon the message if commsSendSemaphore cannot be obtained.

@param char* ident: an identifier string recognized by the receiving program.
@param int32_t param1: first parameter.
@param int32_t param2: second parameter.
*/

void dataMessageSend(char* ident, int32_t param1, int32_t param2)
{
    if (configData.config.measurementSend)
    {
        if (! xSemaphoreTake(commsSendSemaphore,COMMS_SEND_DELAY)) return;
        commsPrintString(ident);
        commsPrintString(",");
        commsPrintInt(param1);
        commsPrintString(",");
        commsPrintInt(param2);
        commsPrintString("\r\n");
        xSemaphoreGive(commsSendSemaphore);
    }
}

/*--------------------------------------------------------------------------*/
/** @brief Send a data message with two parameters at low priority.

This is the same as dataMessageSend except that a message is only sent if the
commsSendQueue is empty.

This blocks indefinitely until the queue is empty of all messages.

@param char* ident: an identifier string recognized by the receiving program.
@param int32_t param1: first parameter.
@param int32_t param2: second parameter.
*/

void dataMessageSendLowPriority(char* ident, int32_t param1, int32_t param2)
{
    if (configData.config.measurementSend)
    {
/* If any characters are on the send queue, block on the commsEmptySemaphore
which is released by the ISR after the last character has been sent. One
message is then sent. The calling task cannot queue more than one message. */
/* Hold indefinitely as the message must not be abandoned */
        while (uxQueueMessagesWaiting(commsSendQueue) > 0)
            xSemaphoreTake(commsEmptySemaphore,portMAX_DELAY);
        if (! xSemaphoreTake(commsSendSemaphore,COMMS_SEND_DELAY)) return;
        commsPrintString(ident);
        commsPrintString(",");
        commsPrintInt(param1);
        commsPrintString(",");
        commsPrintInt(param2);
        commsPrintString("\r\n");
        xSemaphoreGive(commsSendSemaphore);
    }
}

/*--------------------------------------------------------------------------*/
/** @brief Send a data message with one parameter

Use to send a simple response to a command. The calling task will block until
commsSendSemaphore is available.

@param[in] char* ident. Response identifier string
@param[in] int32_t parameter. Single integer parameter.
*/

void sendResponse(char* ident, int32_t parameter)
{
    if (configData.config.measurementSend)
    {
        if (! xSemaphoreTake(commsSendSemaphore,COMMS_SEND_DELAY)) return;
        commsPrintString(ident);
        commsPrintString(",");
        commsPrintInt(parameter);
        commsPrintString("\r\n");
        xSemaphoreGive(commsSendSemaphore);
    }
}

/*--------------------------------------------------------------------------*/
/** @brief Send a data message with one parameter at low priority.

Use to send a simple response to a command. The calling task will block until
commsSendSemaphore is available.

@param[in] char* ident. Response identifier string
@param[in] int32_t parameter. Single integer parameter.
*/

void sendResponseLowPriority(char* ident, int32_t parameter)
{
    if (configData.config.measurementSend)
    {
/* If any characters are on the send queue, block on the commsEmptySemaphore
which is released by the ISR after the last character has been sent. One
message is then sent. The calling task cannot queue more than one message. */
/* Hold indefinitely as the message must not be abandoned */
        while (uxQueueMessagesWaiting(commsSendQueue) > 0)
            xSemaphoreTake(commsEmptySemaphore,portMAX_DELAY);
        if (! xSemaphoreTake(commsSendSemaphore,COMMS_SEND_DELAY)) return;
        commsPrintString(ident);
        commsPrintString(",");
        commsPrintInt(parameter);
        commsPrintString("\r\n");
        xSemaphoreGive(commsSendSemaphore);
    }
}

/*--------------------------------------------------------------------------*/
/** @brief Send a debug message with one parameter at low priority.

Use to send a simple debug response to a command. The calling task will block
until commsSendSemaphore is available.

@param[in] char* ident. Response identifier string
@param[in] int32_t parameter. Single integer parameter.
*/

void sendDebugResponse(char* ident, int32_t parameter)
{
    if ((ident[0] == 'D') && !configData.config.debugMessageSend) return;
/* If any characters are on the send queue, block on the commsEmptySemaphore
which is released by the ISR after the last character has been sent. One
message is then sent. The calling task cannot queue more than one message. */
/* Hold indefinitely as the message must not be abandoned */
    while (uxQueueMessagesWaiting(commsSendQueue) > 0)
        xSemaphoreTake(commsEmptySemaphore,portMAX_DELAY);
    if (! xSemaphoreTake(commsSendSemaphore,COMMS_SEND_DELAY)) return;
    commsPrintString(ident);
    commsPrintString(",");
    commsPrintInt(parameter);
    commsPrintString("\r\n");
    xSemaphoreGive(commsSendSemaphore);
}

/*--------------------------------------------------------------------------*/
/** @brief Send a string

Use to send a string. This simply abandons the message if it cannot get the
commsSendSemaphore.

@param[in] char* ident. Response identifier string
@param[in] int32_t parameter. Single integer parameter.
*/

void sendString(char* ident, char* string)
{
    if (configData.config.measurementSend)
    {
        if (uxQueueSpacesAvailable(commsSendQueue) >=
            stringLength(ident)+stringLength(string)+3)
        {
            if (! xSemaphoreTake(commsSendSemaphore,COMMS_SEND_DELAY)) return;
            commsPrintString(ident);
            commsPrintString(",");
            commsPrintString(string);
            commsPrintString("\r\n");
            xSemaphoreGive(commsSendSemaphore);
        }
    }
}

/*--------------------------------------------------------------------------*/
/** @brief Send a string at low priority.

Use to send a string. A message is only sent if the commsSendQueue is empty.

This blocks indefinitely until the queue is empty of all messages.

@param[in] char* ident. Response identifier string
@param[in] char* string. Arbitrary length string.
*/

void sendStringLowPriority(char* ident, char* string)
{
    if (configData.config.measurementSend)
    {
/* If any characters are on the send queue, block on the commsEmptySemaphore
which is released by the ISR after the last character has been sent. One
message is then sent. The calling task cannot queue more than one message. */
/* Hold indefinitely as the message must not be abandoned */
        if (uxQueueSpacesAvailable(commsSendQueue) >=
            stringLength(ident)+stringLength(string)+3)
        {
            while (uxQueueMessagesWaiting(commsSendQueue) > 0)
                xSemaphoreTake(commsEmptySemaphore,portMAX_DELAY);
            xSemaphoreTake(commsSendSemaphore,portMAX_DELAY);
            commsPrintString(ident);
            commsPrintString(",");
            commsPrintString(string);
            commsPrintString("\r\n");
            xSemaphoreGive(commsSendSemaphore);
        }
    }
}

/*--------------------------------------------------------------------------*/
/** @brief Send a debug string at low priority.

Use to send a debug string. A message is only sent if the commsSendQueue is
empty and the debug messages are enabled.

This blocks indefinitely until the queue is empty of all messages.

@param[in] char* ident. Response identifier string
@param[in] int32_t parameter. Single integer parameter.
*/

void sendDebugString(char* ident, char* string)
{
    if ((ident[0] == 'D') && !configData.config.debugMessageSend) return;
/* If any characters are on the send queue, block on the commsEmptySemaphore
which is released by the ISR after the last character has been sent. One
message is then sent. The calling task cannot queue more than one message. */
/* Hold indefinitely as the message must not be abandoned */
    if (uxQueueSpacesAvailable(commsSendQueue) >=
        stringLength(ident)+stringLength(string)+3)
    {
        while (uxQueueMessagesWaiting(commsSendQueue) > 0)
            xSemaphoreTake(commsEmptySemaphore,portMAX_DELAY);
        xSemaphoreTake(commsSendSemaphore,portMAX_DELAY);
        commsPrintString(ident);
        commsPrintString(",");
        commsPrintString(string);
        commsPrintString("\r\n");
        xSemaphoreGive(commsSendSemaphore);
    }
}

/*--------------------------------------------------------------------------*/
/** @brief Print out the contents of a register (debug)

@param[in] uint32_t reg: full address of register.

*/

void commsPrintRegister(uint32_t reg)
{
    if (uxQueueSpacesAvailable(commsSendQueue) >= 11)
    {
        commsPrintHex((reg >> 16) & 0xFFFF);
        commsPrintHex((reg >> 00) & 0xFFFF);
        commsPrintChar(" ");
    }
}

/*--------------------------------------------------------------------------*/
/** @brief Print out a value in ASCII decimal form (ack Thomas Otto)

@param[in] int32_t value: integer value to be printed.
*/

void commsPrintInt(int32_t value)
{
    uint8_t i=0;
    char buffer[25];
    intToAscii(value, buffer);
    if (uxQueueSpacesAvailable(commsSendQueue) >= stringLength(buffer))
        while (buffer[i] > 0)
        {
            commsPrintChar(&buffer[i]);
            i++;
        }
}

/*--------------------------------------------------------------------------*/
/** @brief Print out a value in 16 bit ASCII hex form

@param[in] int32_t value: integer value to be printed.
*/

void commsPrintHex(uint32_t value)
{
    uint8_t i;
    char buffer[25];

    for (i = 0; i < 4; i++)
    {
        buffer[i] = "0123456789ABCDEF"[value & 0xF];
        value >>= 4;
    }
    if (uxQueueSpacesAvailable(commsSendQueue) >= 5)
    {
        for (i = 4; i > 0; i--)
        {
            commsPrintChar(&buffer[i-1]);
        }
/*    commsPrintChar(" "); */
    }
}

/*--------------------------------------------------------------------------*/
/** @brief Print a String

@param[in] char *ch: pointer to string to be printed.
*/

void commsPrintString(char *ch)
{
    if (uxQueueSpacesAvailable(commsSendQueue) >= stringLength(ch))
        while(*ch) commsPrintChar(ch++);
}

/*--------------------------------------------------------------------------*/
/** @brief Print a Character

Disable the Tx interrupt first to prevent queue corruption in the ISR.
This is where the characters are queued for the ISR to transmit.
The ISR is in the hardware module.

Characters are placed on a queue and picked up by the ISR for transmission.
The application is responsible for protecting a message with semaphores
to ensure it is sent in entirety (see convenience functions defined here).

If the queue fails to respond it is reset. A number of messages will be lost but
hopefully the application will continue to run. A receiving program may see
a corrupted message.

@param[in] char *ch: pointer to character to be printed.
*/

void commsPrintChar(char *ch)
{
    if (configData.config.enableSend)
    {
        commsEnableTxInterrupt(false);
        while (xQueueSendToBack(commsSendQueue,ch,COMMS_SEND_TIMEOUT) != pdTRUE)
        {
            xQueueReset(commsSendQueue);
            commsEnableTxInterrupt(true);
            taskYIELD();
        }
        commsEnableTxInterrupt(true);
    }
}

/*--------------------------------------------------------------------------*/
/** @brief Callback function to lapse communications

This is called if the lapse communications timer is not reset by a received
message within the timeout period. The GUI is expected to regularly send a
message of some sort to keep communications alive. This feature allows
power hungry communications circuits to be used only when the GUI is open.
*/

void lapseCommsCallback(xTimerHandle lapseCommsTimer)
{
    configData.config.enableSend = false;    
}
