dmsherazi/Battery-Management-System/firmware/power-management-time.c

/* STM32F1 Power Management for Solar Power

Defines the time and date counter to carry the real time count in seconds for
time stamping of records. Access functions are provided for setting from a UTC
string and reading to a string.

Initial 25 November 2013
*/

/*
 * This file is part of the battery-management-system project.
 *
 * Copyright 2013 K. Sarkies <ksarkies@internode.on.net>
 *
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
 * You should have received a copy of the GNU Lesser General Public License
 * along with this program.  If not, see <http://www.gnu.org/licenses/>.
 */

#include <stdint.h>
#include <stdbool.h>
#include <time.h>

#include "power-management-objdic.h"
#include "power-management-hardware.h"
#include "power-management-lib.h"
#include "power-management-time.h"
#include "power-management-comms.h"

/*--------------------------------------------------------------------------*/
/* @brief Return a string containing the time and date

Convert the global time to an ISO 8601 string.

@param[out] timeString char*. Returns pointer to string with formatted date.
*/

void putTimeToString(char* timeString)
{
    time_t currentTime = (time_t)getTimeCounter();
    struct tm *rtc = localtime(&currentTime);
//    strftime(timeString, sizeof timeString, "%FT%TZ", rtc);
    char buffer[10];
    intToAscii(rtc->tm_year+1900, timeString);
    stringAppend(timeString,"-");
    if (rtc->tm_mon < 9) stringAppend(timeString,"0");
    intToAscii(rtc->tm_mon+1, buffer);
    stringAppend(timeString,buffer);
    stringAppend(timeString,"-");
    if (rtc->tm_mday < 10) stringAppend(timeString,"0");
    intToAscii(rtc->tm_mday, buffer);
    stringAppend(timeString,buffer);
    stringAppend(timeString,"T");
    if (rtc->tm_hour < 10) stringAppend(timeString,"0");
    intToAscii(rtc->tm_hour, buffer);
    stringAppend(timeString,buffer);
    stringAppend(timeString,":");
    if (rtc->tm_min < 10) stringAppend(timeString,"0");
    intToAscii(rtc->tm_min, buffer);
    stringAppend(timeString,buffer);
    stringAppend(timeString,":");
    if (rtc->tm_sec < 10) stringAppend(timeString,"0");
    intToAscii(rtc->tm_sec, buffer);
    stringAppend(timeString,buffer);
}

/*--------------------------------------------------------------------------*/
/* @brief Set the time variable from an ISO 8601 formatted date/time

@param[in] timeString: pointer to string with formatted date.
*/

void setTimeFromString(char* timeString)
{
    struct tm newTime;
    char buffer[5];
    uint8_t i;

    for (i=0; i<4; i++) buffer[i] = timeString[i];
    buffer[4] = 0;
    newTime.tm_year = asciiToInt(buffer)-1900;
    for (i=0; i<2; i++) buffer[i] = timeString[i+5];
    buffer[2] = 0;
    newTime.tm_mon = asciiToInt(buffer)-1;
    for (i=0; i<2; i++) buffer[i] = timeString[i+8];
    newTime.tm_mday = asciiToInt(buffer);
    for (i=0; i<2; i++) buffer[i] = timeString[i+11];
    newTime.tm_hour = asciiToInt(buffer);
    for (i=0; i<2; i++) buffer[i] = timeString[i+14];
    newTime.tm_min = asciiToInt(buffer);
    for (i=0; i<2; i++) buffer[i] = timeString[i+17];
    newTime.tm_sec = asciiToInt(buffer);

    setTimeCounter((uint32_t)mktime(&newTime));
}
